odelot/nes-ra-adapter/images/case-cartridge-back.png

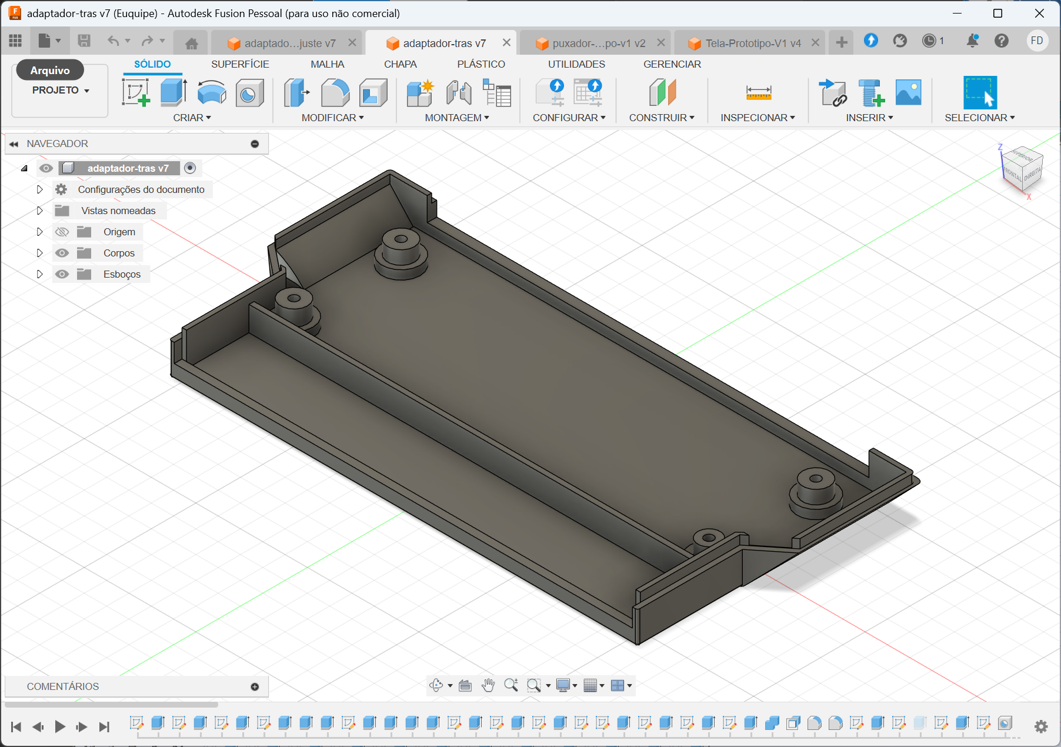
images/case-cartridge-back.png
