odelot/nes-ra-adapter/images/case-cartridge-front.png

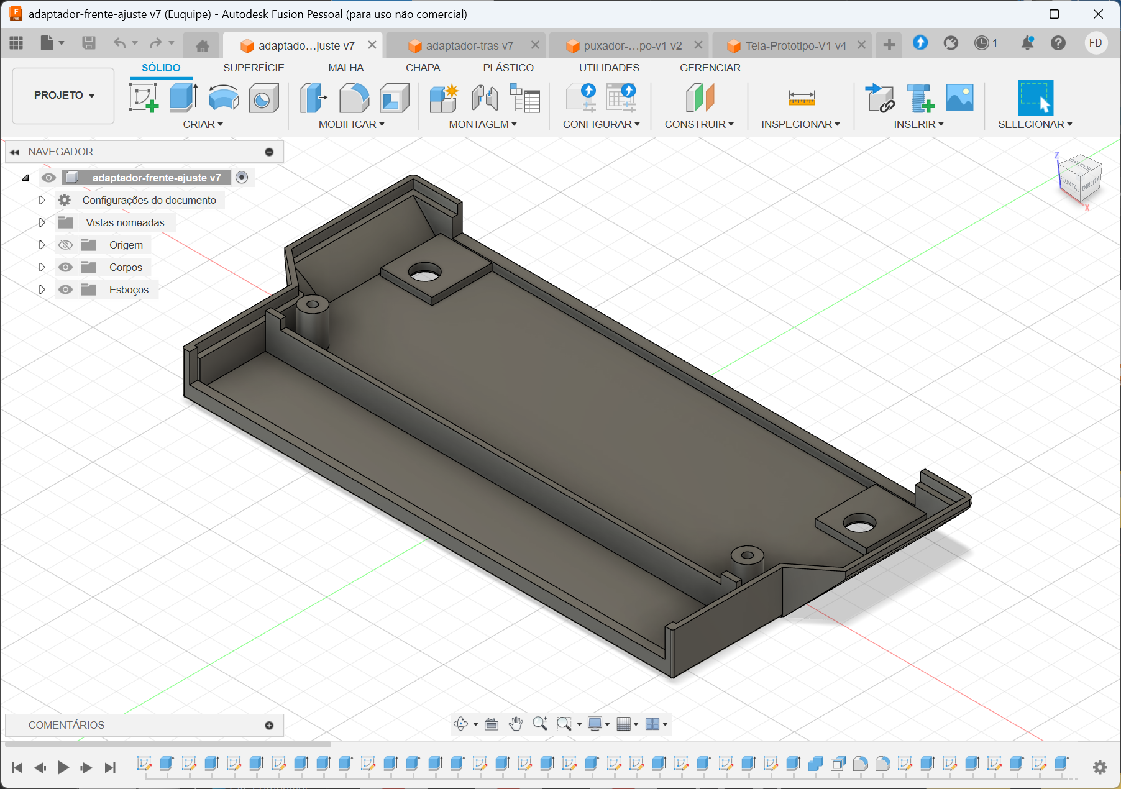
images/case-cartridge-front.png
